FaBoAI/Matrix6/docs/devboard-v04/review/pcb-3d-v04.png

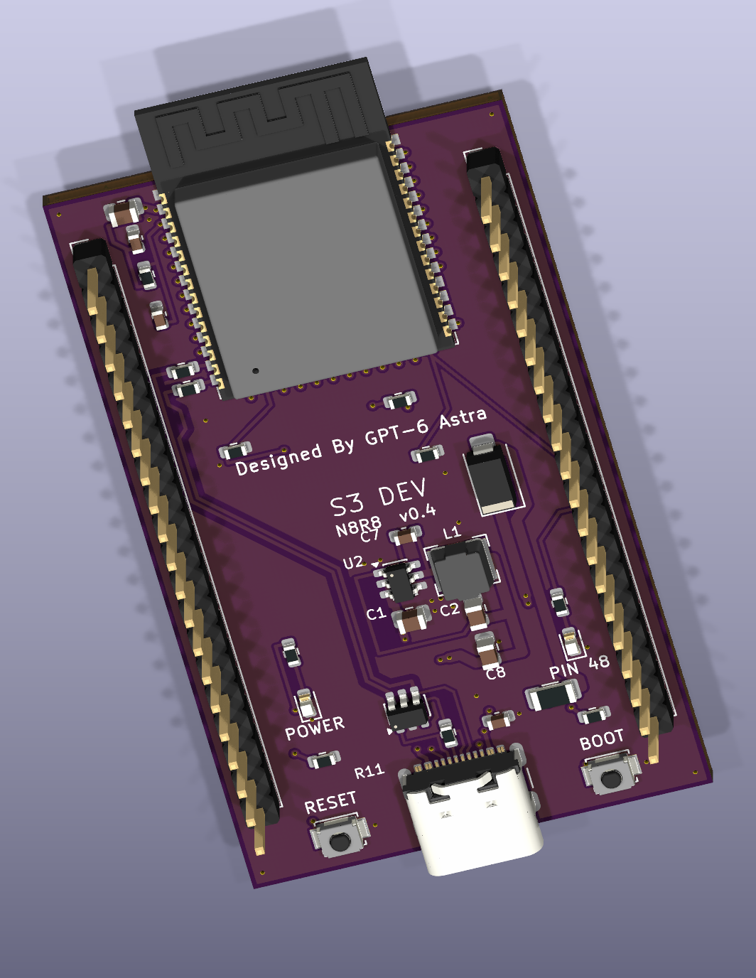
docs/devboard-v04/review/pcb-3d-v04.png
