FaBoAI/Matrix6/docs/devboard-v04/review/pcb-top-v04.png

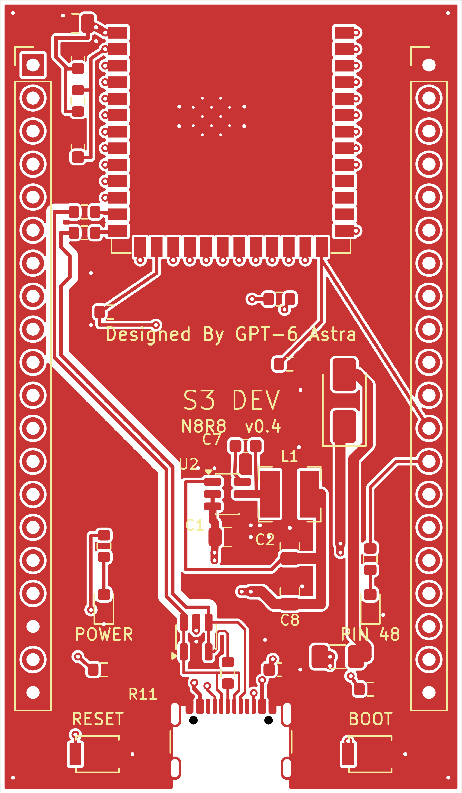
docs/devboard-v04/review/pcb-top-v04.png
