FaBoAI/Matrix6/docs/validation/pcb-3d.png

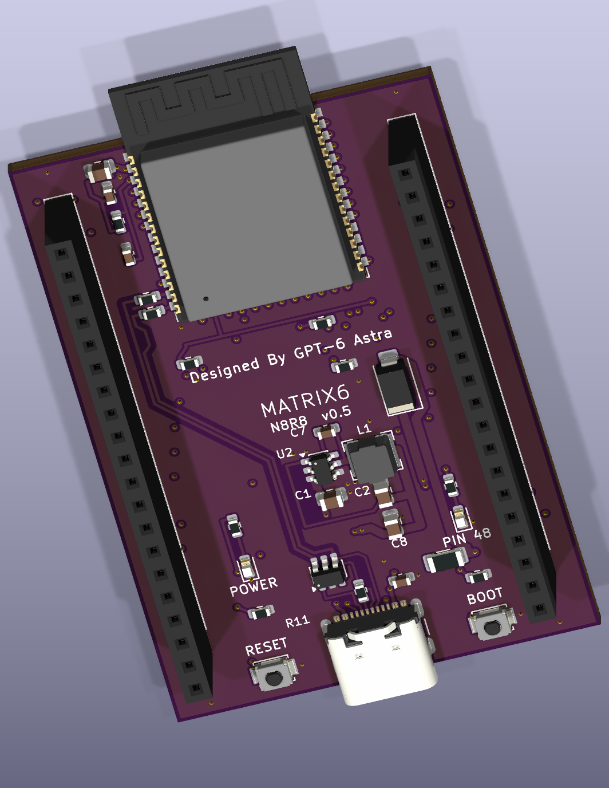
docs/validation/pcb-3d.png
