FaBoAI/Matrix6/docs/validation/pcb-top.png

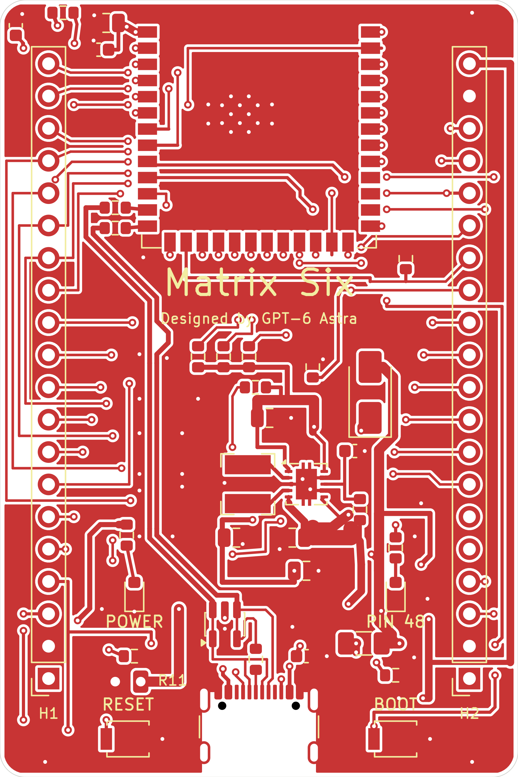
docs/validation/pcb-top.png
