FaBoAI/Matrix6/docs/validation/sd-access.png

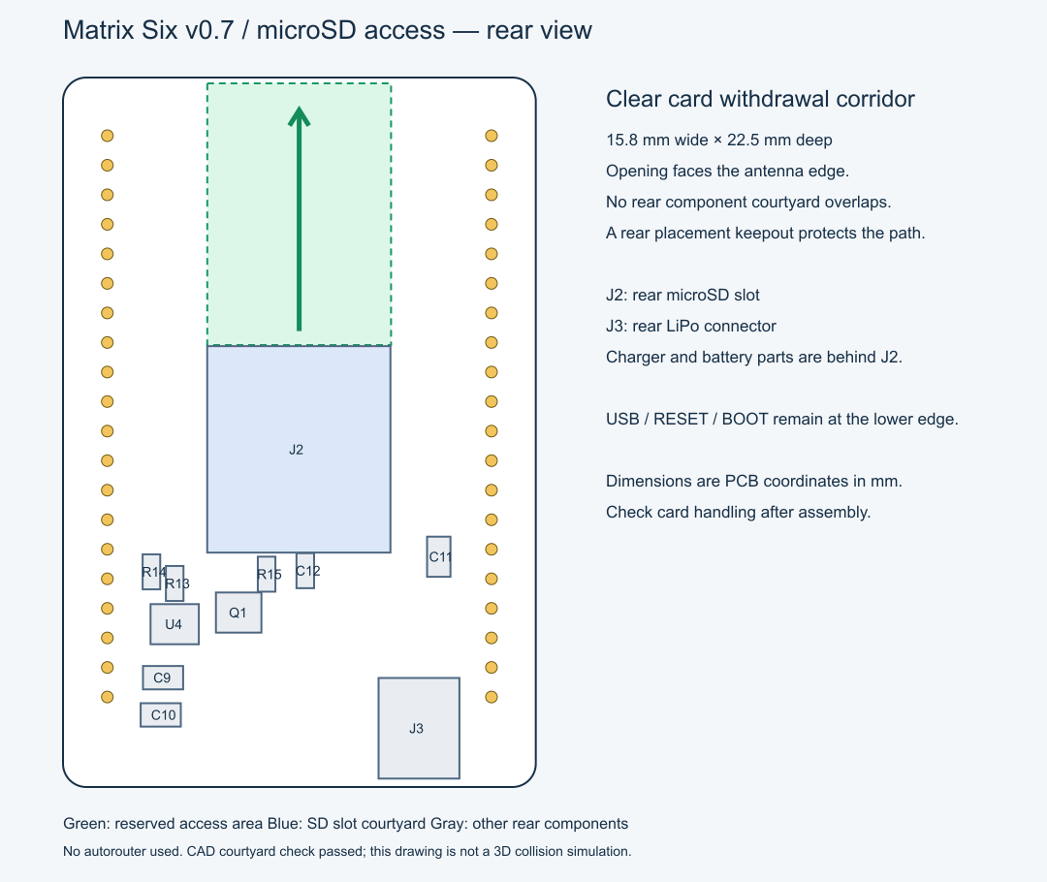
docs/validation/sd-access.png
